deebuggertech/PhyESPx/additional_resources/wiring_diagram/wiring_complete.png

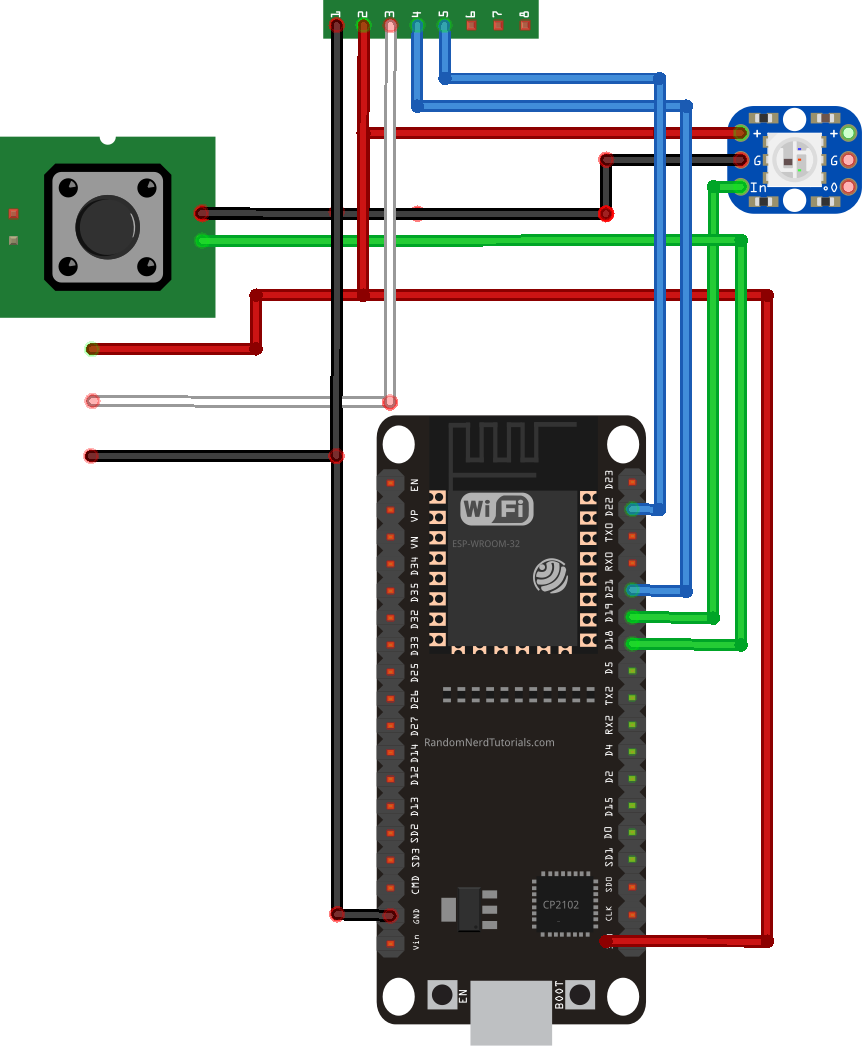
additional_resources/wiring_diagram/wiring_complete.png
